tsar-boomba/dap-proto-board-full/In2.Cu.png

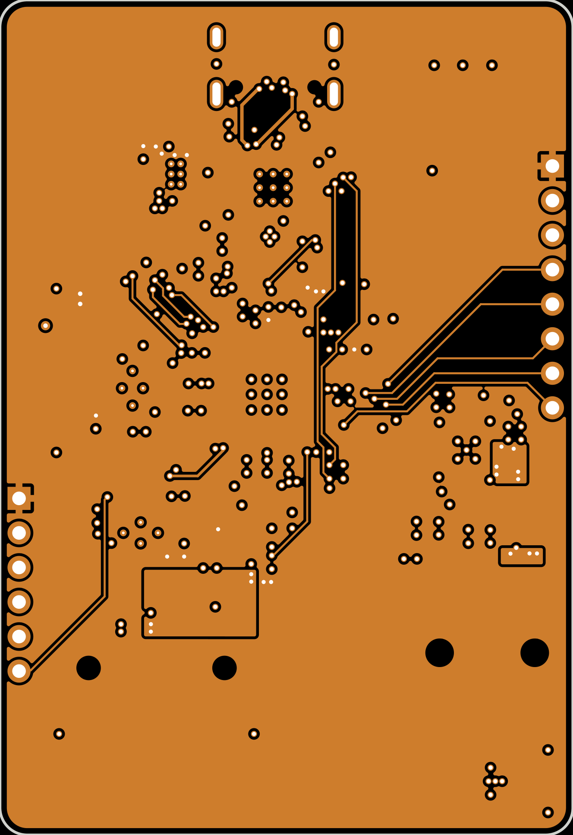
In2.Cu.png
